The-Young-Maker/DIY-Tiny-ESP32-NAS/Code/router.ino

/*

    Router.ino

    This is the main router of the whole web server.
    It is like the apache.conf where you handle routing
    to different services.

    By default, all route will go to the SD card /www/ folder
*/
void serveStaticFile(AsyncWebServerRequest *request, const String &filePath, const String &mimeType) {
  File dataFile = SD.open(filePath.c_str());

  if (dataFile) {
    if (request->hasArg("download")) {
      // Set the appropriate content type for download
      request->send(SD, filePath, "application/octet-stream");
    } else {
      // Stream the file with the specified MIME type
      request->send(SD, filePath, mimeType);
    }
    dataFile.close();
  } else {
    // Handle the case where the file doesn't exist
    request->send(404, "text/plain", "File not found");
  }
}

class MainRouter : public AsyncWebHandler {
public:
  MainRouter() {}
  virtual ~MainRouter() {}

  bool canHandle(AsyncWebServerRequest *request) {
    String requestURI = request->url().c_str();
    if (requestURI.equals("/upload")) {
      //File Upload Endpoint
      return false;
    } else if (requestURI.startsWith("/api/")) {
      //API paths
      return false;
    }
    return true;
  }

  //Main Routing Logic Here
  void handleRequest(AsyncWebServerRequest *request) {
    String requestURI = request->url().c_str();

    /* Rewrite the request path if URI contains ./ */
    if (requestURI.indexOf("./") > 0) {
      requestURI.replace("./", "");
      AsyncWebServerResponse *response = request->beginResponse(307);
      response->addHeader("Cache-Control", "no-cache");
      response->addHeader("Location", requestURI);
      request->send(response);
      return;
    }

    /* Special Routing Rules */
    //Redirect / back to index.html
    if (requestURI == "/") {
      request->redirect("/index.html");
      return;
    }

    //Special interfaces that require access controls
    if (requestURI.startsWith("/store/")) {
      //Private file storage. Not allow access
      AsyncWebServerResponse *response = request->beginResponse(401, "text/html", "403 - Forbidden");
      request->send(response);
      return;
    }

    /* Default Routing Rules */

    Serial.println("URI: " + requestURI + " | MIME: " + getMime(requestURI));
    //Check if the file exists on the SD card
    if (SD.exists("/www" + requestURI)) {
      // File exists on the SD card web root
      String fullPath = "/www" + requestURI;

      if (IsDir(fullPath)) {
        String indexPath = fullPath + "index.html";

        if (SD.exists(indexPath.c_str())) {
          // Serve the index.html file
          String mimeType = getMime("index.html");
          serveStaticFile(request, indexPath, mimeType);
        } else {
          // Handle directory rendering here (you can call your custom function)
          HandleDirRender(request, requestURI, fullPath);
        }
      } else {
        // Serve a file based on its MIME type
        String mimeType = getMime(requestURI);
        serveStaticFile(request, fullPath, mimeType);
      }
    } else {
      // File does not exist in web root
      AsyncResponseStream *response = request->beginResponseStream("text/html");
      Serial.println("NOT FOUND: " + requestURI);
      prettyPrintRequest(request);
      response->print("<!DOCTYPE html><html><head><title>Not Found</title></head><body>");
      response->print("<p>404 - Not Found</p>");
      response->printf("<p>Requesting http://%s with URI: %s</p>", request->host().c_str(), request->url().c_str());
      response->print("</body></html>");
      request->send(response);
    }
  }
};
